magape/Fifi/3D/img/fifi_crossv_hatch.png

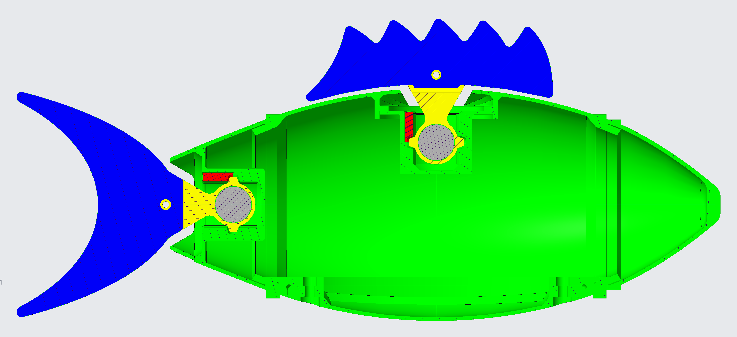
3D/img/fifi_crossv_hatch.png
