magape/Fifi/3D/img/magnetic_actuator_3d_ext.png

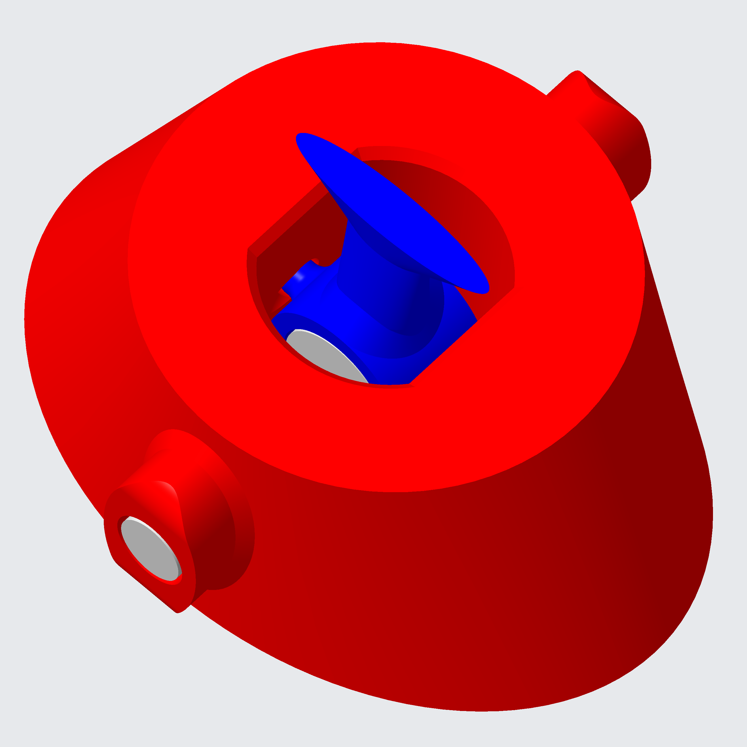
3D/img/magnetic_actuator_3d_ext.png
