magape/Fifi/3D/img/magnetic_actuator_crossV.png

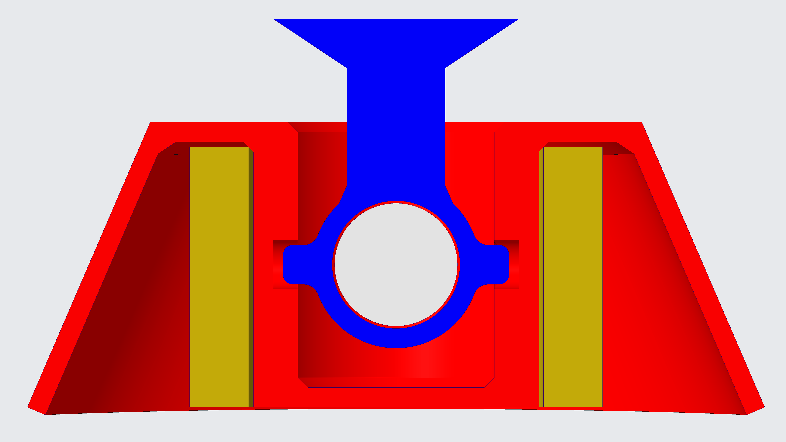
3D/img/magnetic_actuator_crossV.png
