magape/Fifi/etc/IMG_20210411_162028.jpg

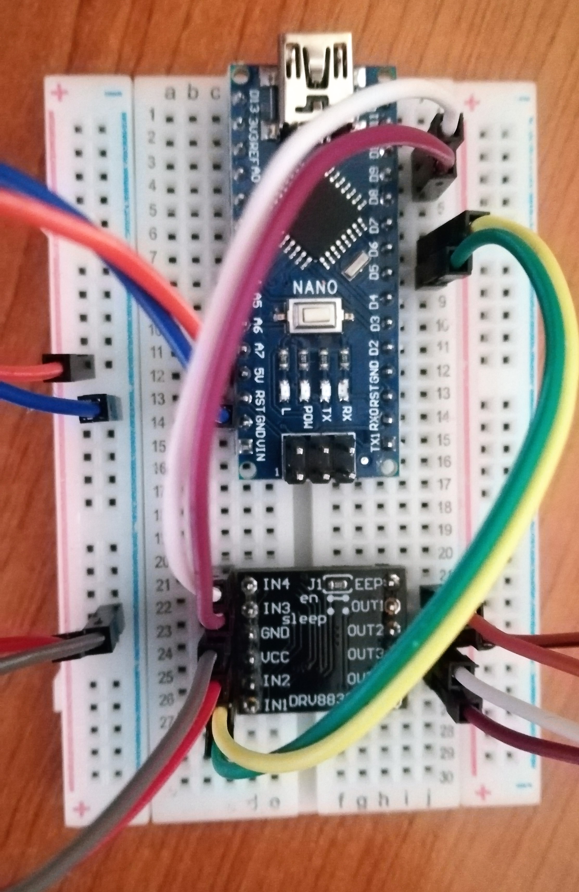
etc/IMG_20210411_162028.jpg
