magape/Fifi/etc/IMG_20210411_173045.jpg

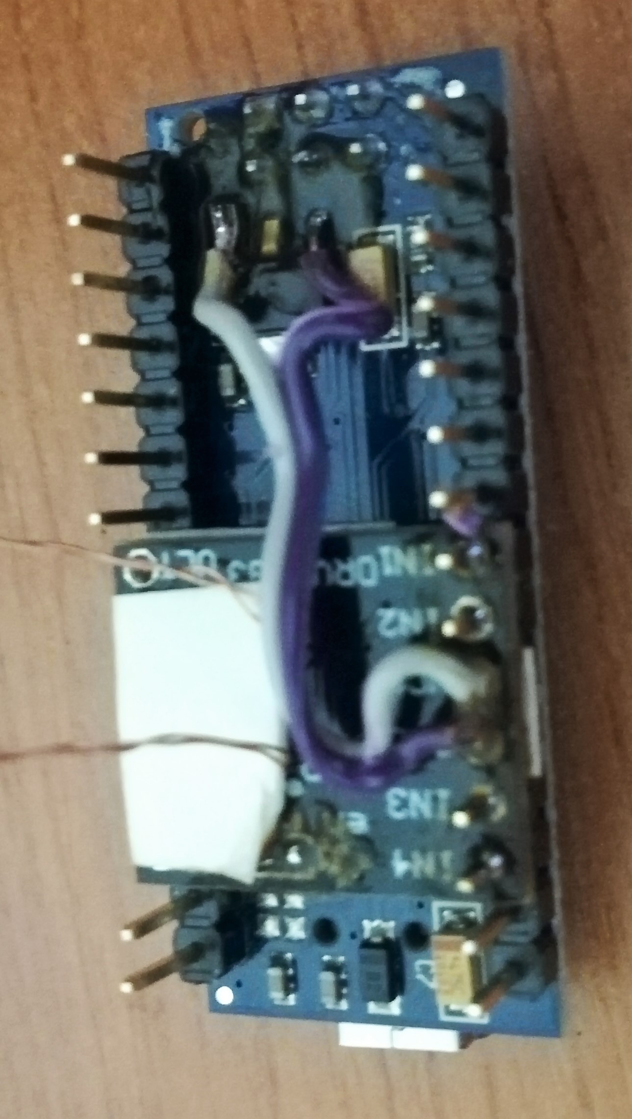
etc/IMG_20210411_173045.jpg
