magape/Fifi/img/Caudal Actuator.jpg

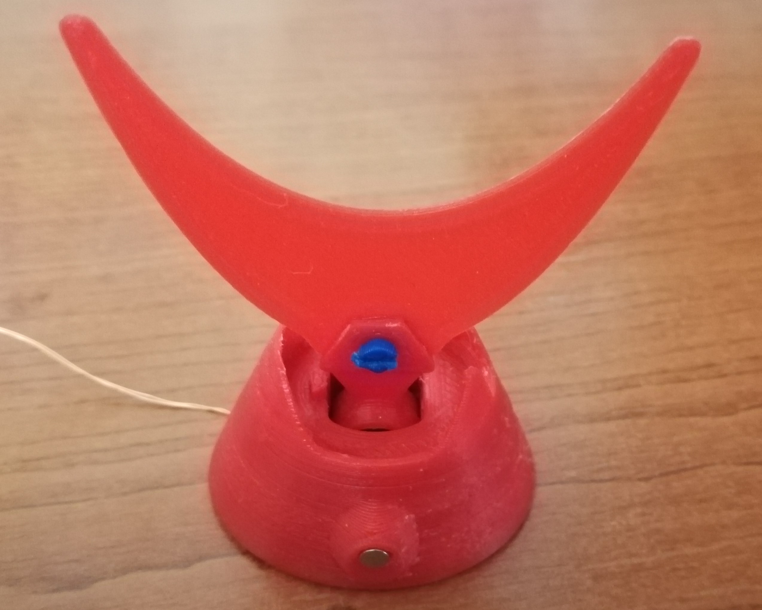
img/Caudal Actuator.jpg
