magape/Fifi/img/IMG_20210314_221234.jpg

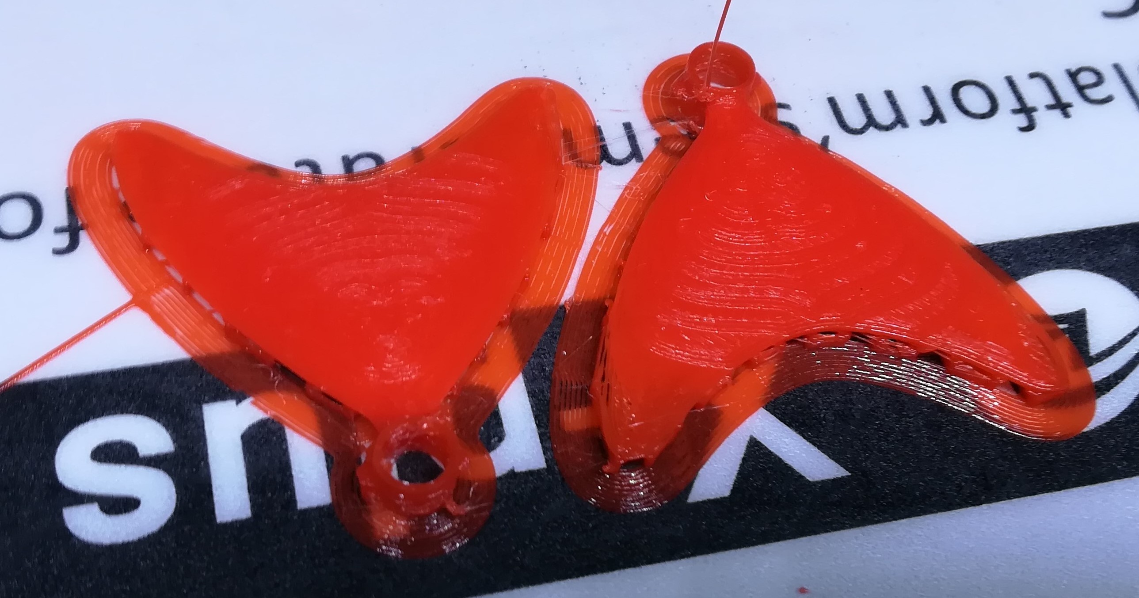
img/IMG_20210314_221234.jpg
