magape/Fifi/img/IMG_20210321_102429.jpg

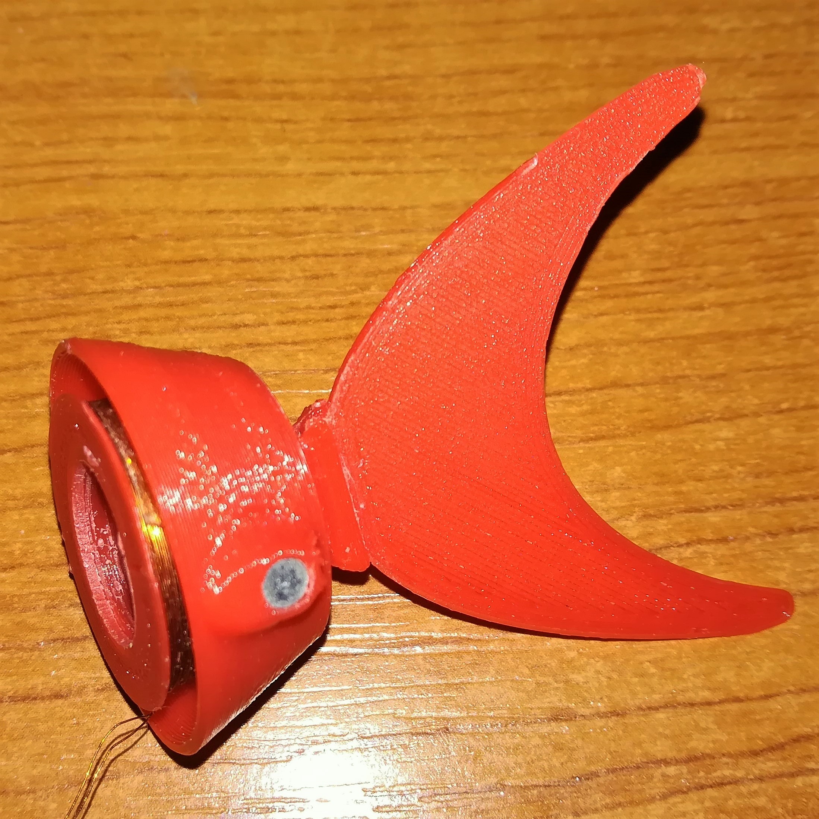
img/IMG_20210321_102429.jpg
