magape/Fifi/img/IMG_20210402_220259.jpg

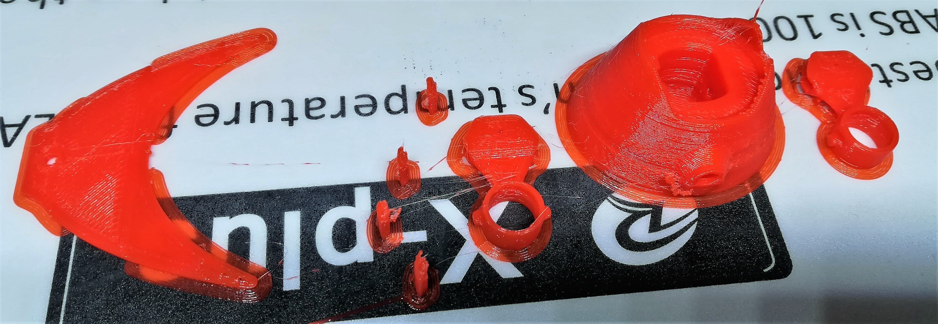
img/IMG_20210402_220259.jpg
