magape/Fifi/img/IMG_20210404_232646.jpg

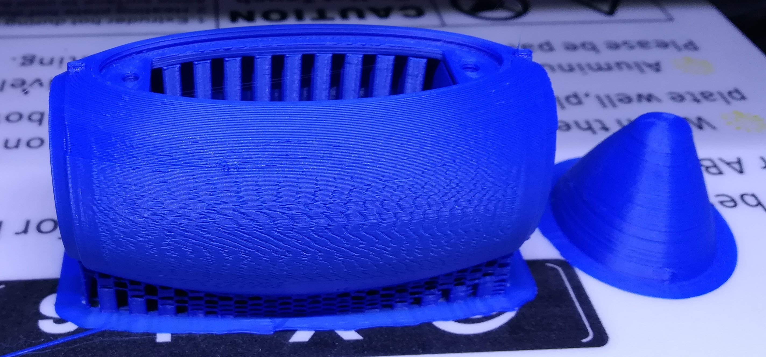
img/IMG_20210404_232646.jpg
