magape/Fifi/img/IMG_20210404_232836.jpg

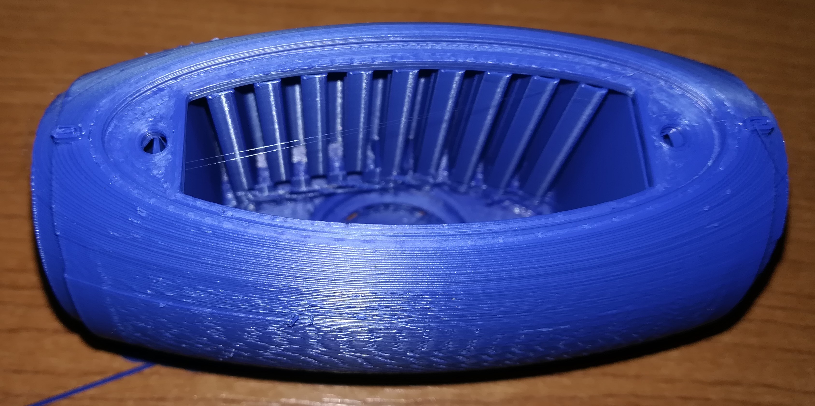
img/IMG_20210404_232836.jpg
