magape/Fifi/img/IMG_20210404_232851.jpg

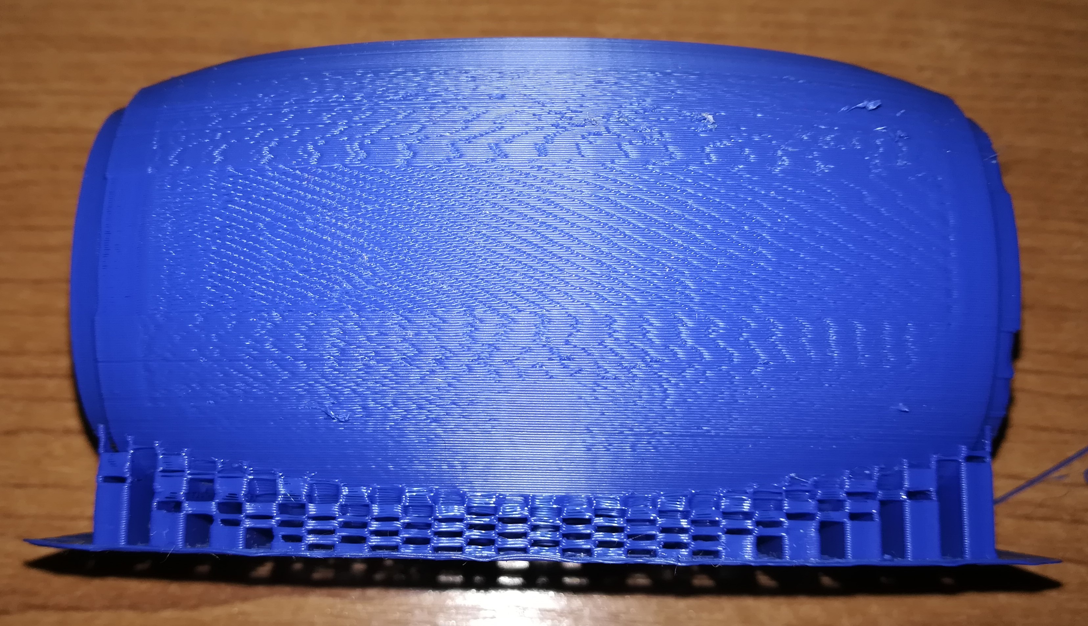
img/IMG_20210404_232851.jpg
