magape/Fifi/img/IMG_20210404_232947.jpg

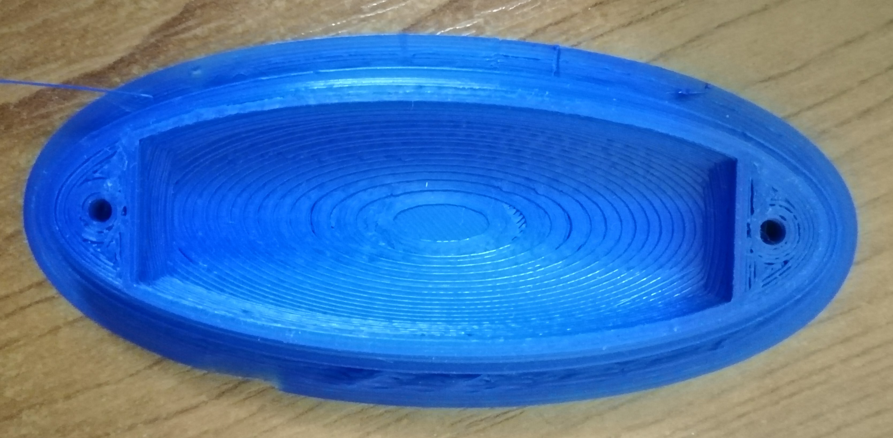
img/IMG_20210404_232947.jpg
