magape/Fifi/img/IMG_20210404_232959.jpg

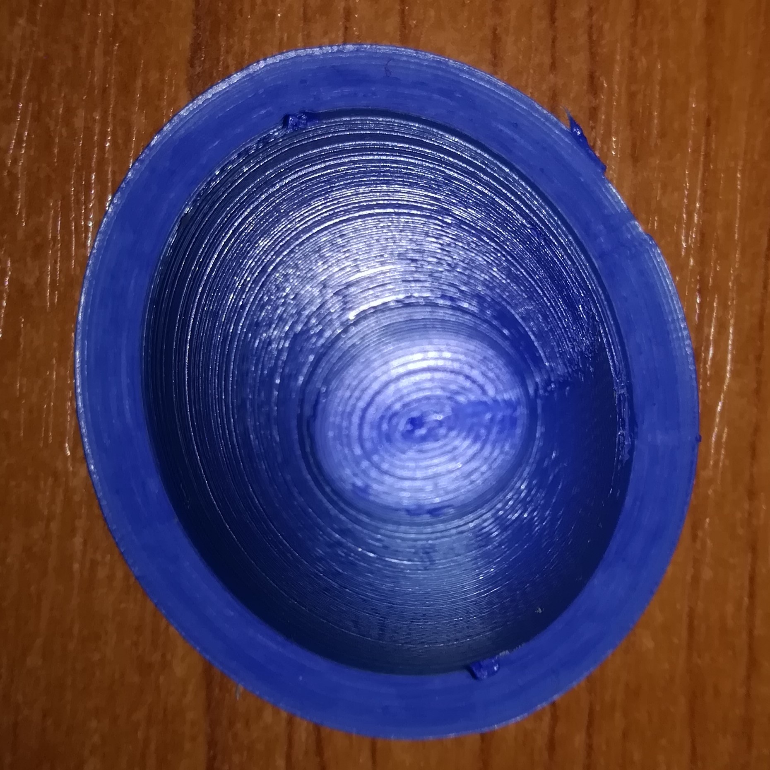
img/IMG_20210404_232959.jpg
