magape/Fifi/img/IMG_20210410_092914.jpg

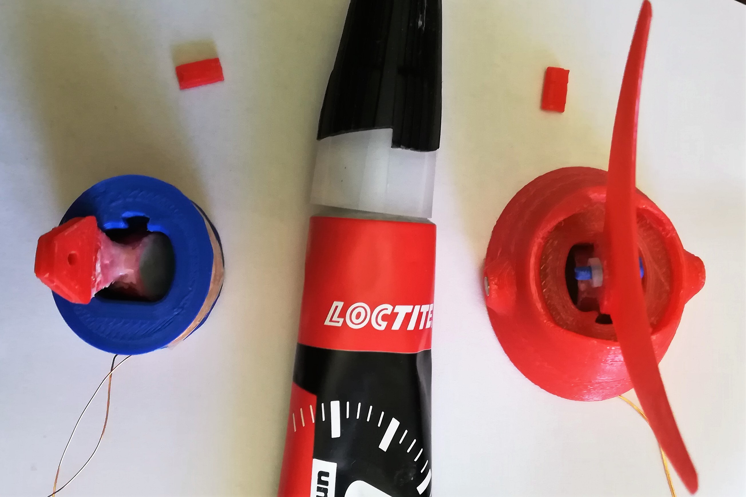
img/IMG_20210410_092914.jpg
