magape/Fifi/img/IMG_20210410_093526.jpg

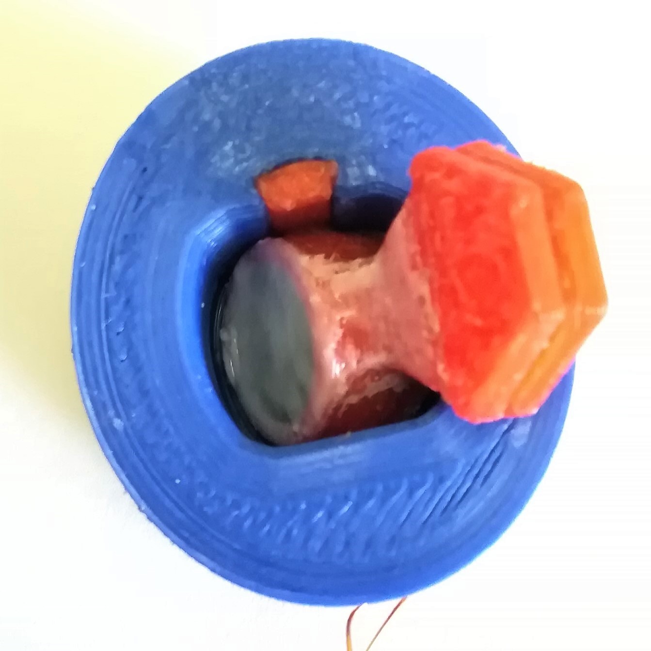
img/IMG_20210410_093526.jpg
