magape/Fifi/img/IMG_20210411_184013.jpg

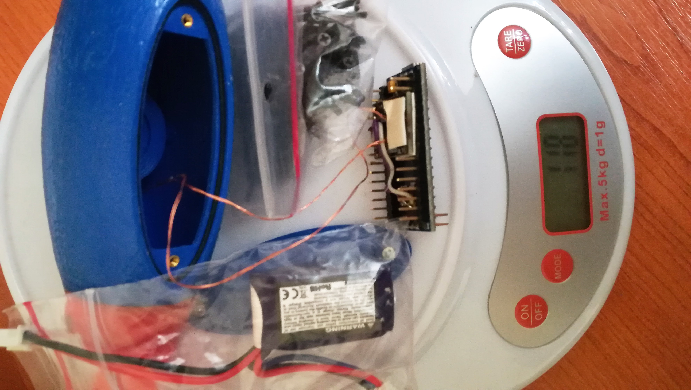
img/IMG_20210411_184013.jpg
