magape/Fifi/img/IMG_20210513_100041.jpg

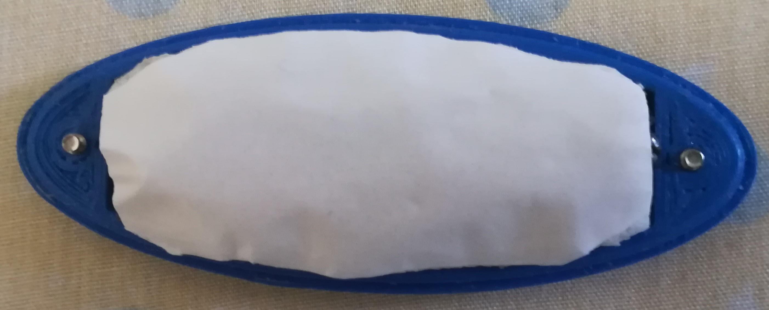
img/IMG_20210513_100041.jpg
