magape/Fifi/img/IMG_20210517_120248.jpg

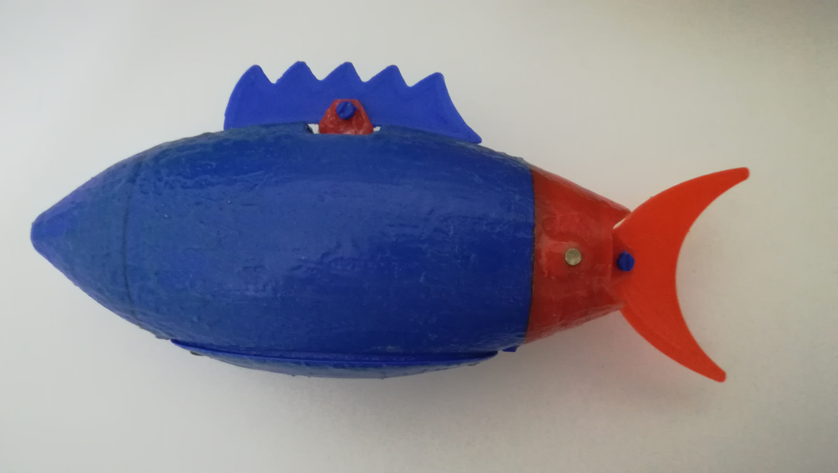
img/IMG_20210517_120248.jpg
